jebentancour/Bandonberry/stl/CodificacionDeNombresDePartea.jpg

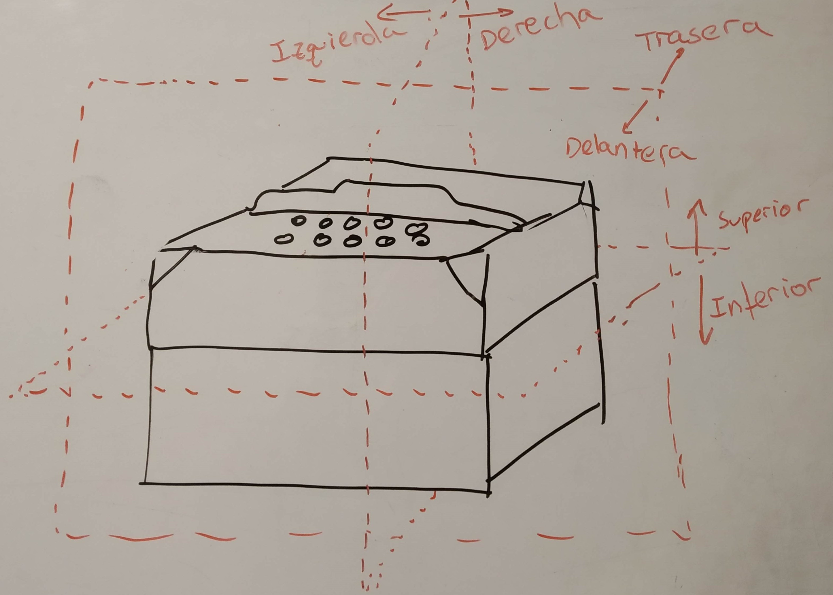
stl/CodificacionDeNombresDePartea.jpg
