jebentancour/Bandonberry/stl/FotosConMedidas/FotoMedida2.png

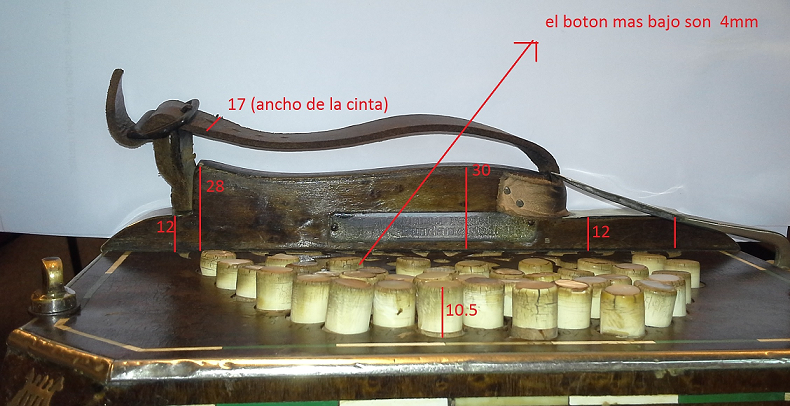
stl/FotosConMedidas/FotoMedida2.png
