jebentancour/Bandonberry/stl/FotosConMedidas/FotoMedida7.png

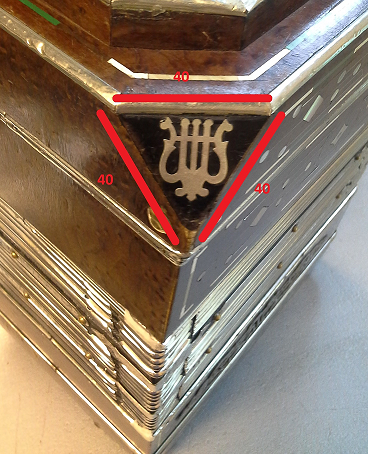
stl/FotosConMedidas/FotoMedida7.png
