jebentancour/Bandonberry/stl/FotosConMedidas/FotoMedida8.png

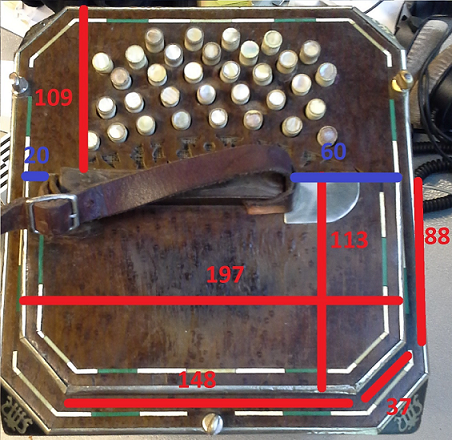
stl/FotosConMedidas/FotoMedida8.png
