jebentancour/Bandonberry/stl/STL_Tapa_Derecha/Botonera.stl

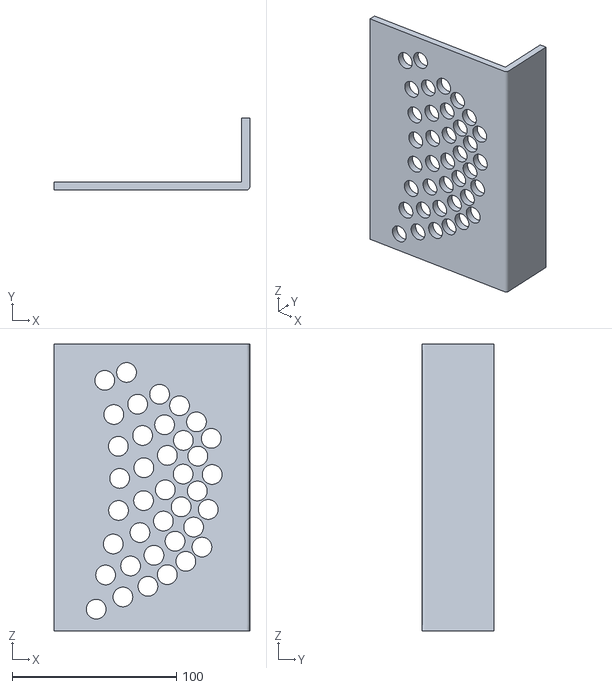
[picture p38: CAD file, 2019-04-07]
stl/STL_Tapa_Derecha/Botonera.stl
119.0 x 43.8 x 174.6
