jebentancour/Bandonberry/stl/STL_Tapa_Izquierda/EsqInfDelIzq.stl

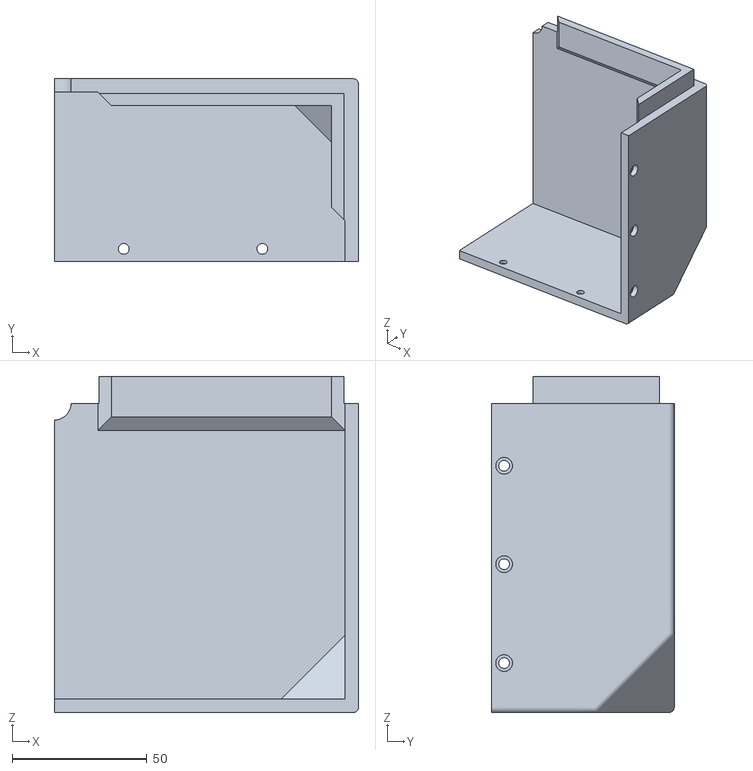
[picture p39: CAD file, 2019-04-07]
stl/STL_Tapa_Izquierda/EsqInfDelIzq.stl
112.9 x 67.8 x 124.8
