jebentancour/Bandonberry/stl/Agarres_Botones/Agarres/AgarreTuercaSimple.stl

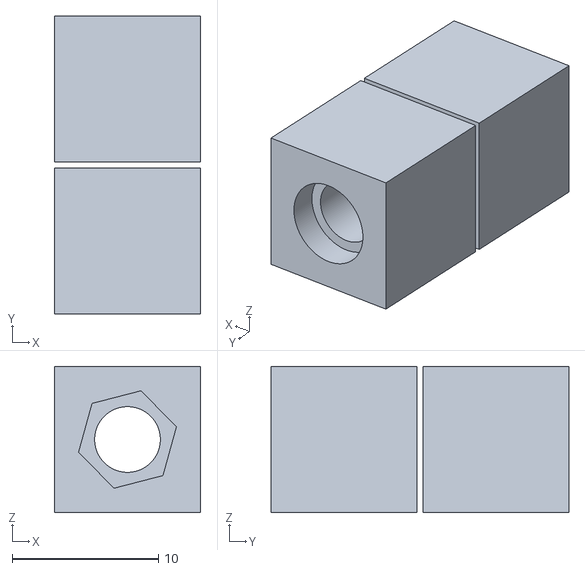
[picture p40: CAD file, 2019-04-07]
stl/Agarres_Botones/Agarres/AgarreTuercaSimple.stl
10.0 x 20.4 x 10.0
