jebentancour/Bandonberry/stl/STL_Tapa_Derecha/EsqIzqTrasInf.stl

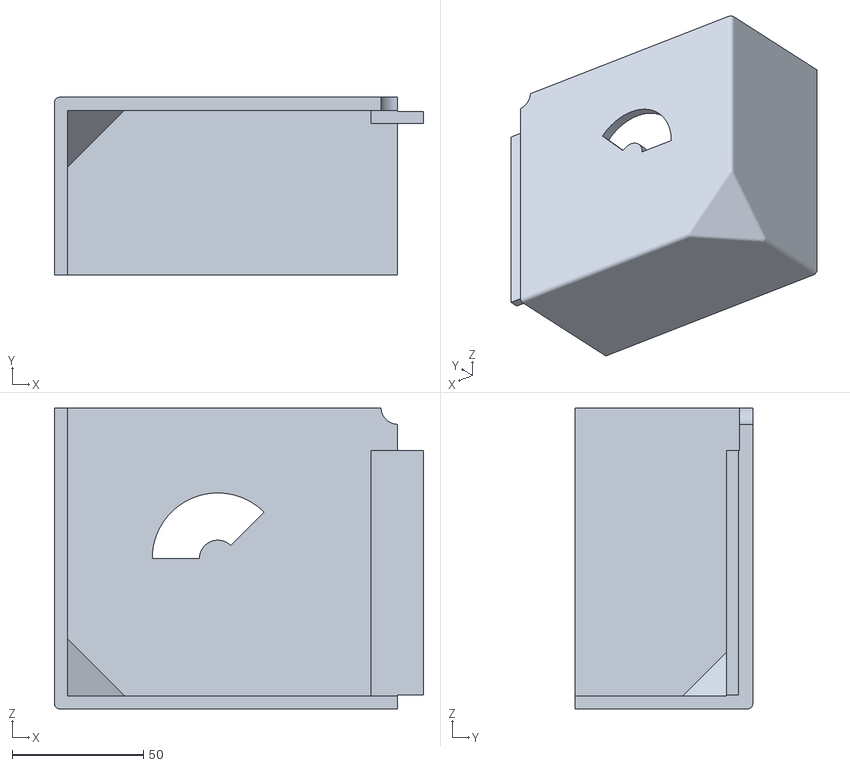
[picture p41: CAD file, 2019-04-07]
stl/STL_Tapa_Derecha/EsqIzqTrasInf.stl
140.8 x 67.8 x 114.8
