jebentancour/Bandonberry/stl/STL_Tapa_Izquierda/EsqSupTrasIzq.stl

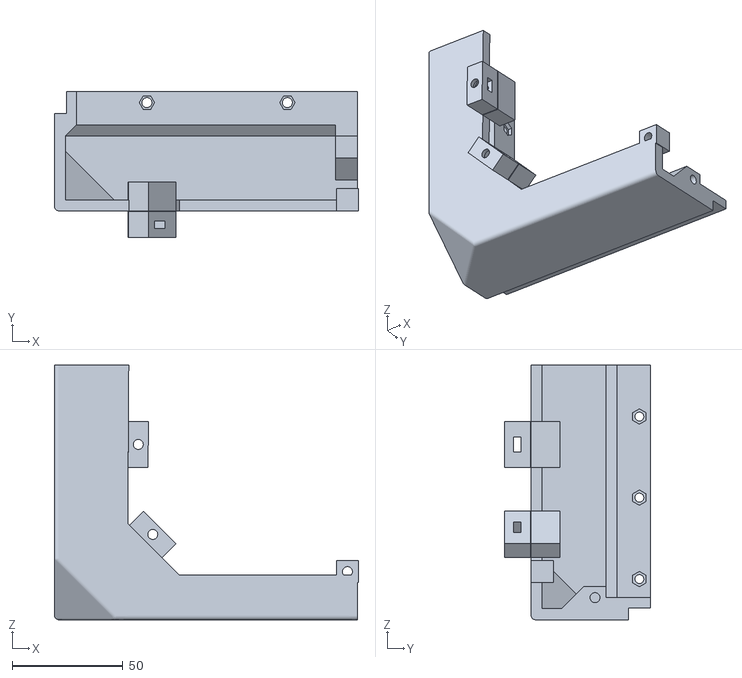
[picture p42: CAD file, 2019-04-07]
stl/STL_Tapa_Izquierda/EsqSupTrasIzq.stl
137.1 x 65.8 x 114.8
