jebentancour/Bandonberry/stl/STL_Tapa_Derecha/EsqDerDelInf.stl

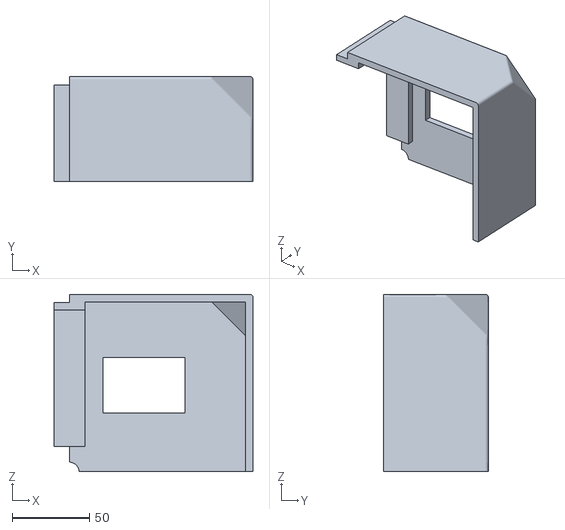
[picture p43: CAD file, 2019-04-07]
stl/STL_Tapa_Derecha/EsqDerDelInf.stl
128.8 x 67.8 x 114.8
