jebentancour/Bandonberry/stl/STL_Tapa_Izquierda/EsqInfDelDer.stl

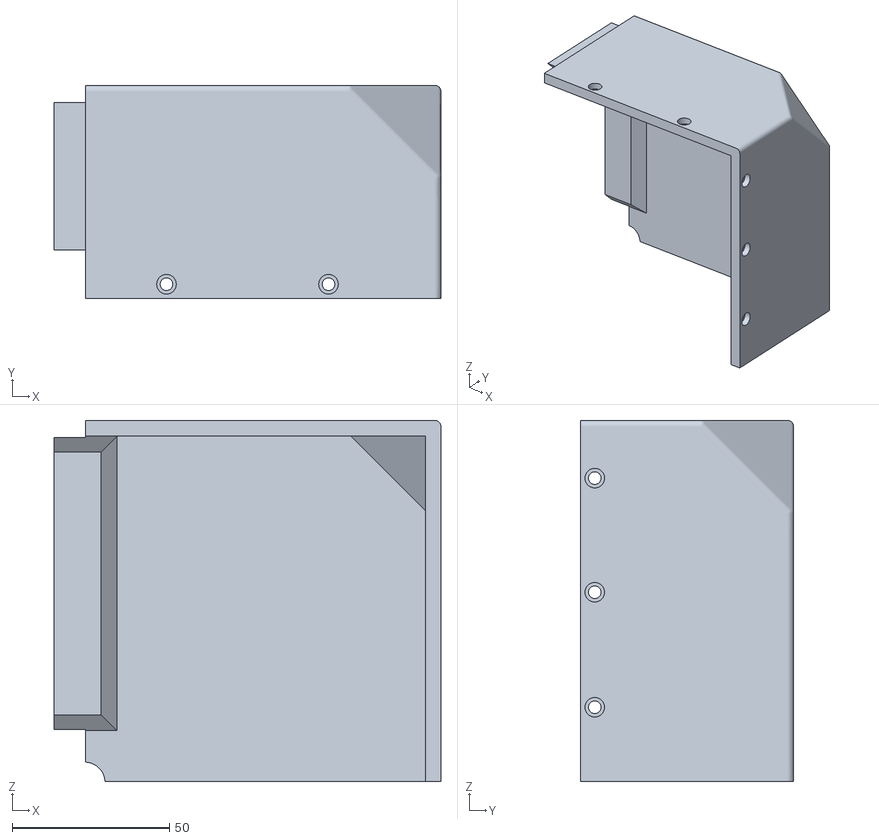
[picture p44: CAD file, 2019-04-07]
stl/STL_Tapa_Izquierda/EsqInfDelDer.stl
122.9 x 67.8 x 114.8
