jebentancour/Bandonberry/stl/STL_Tapa_Derecha/EsqDerTrasInf.stl

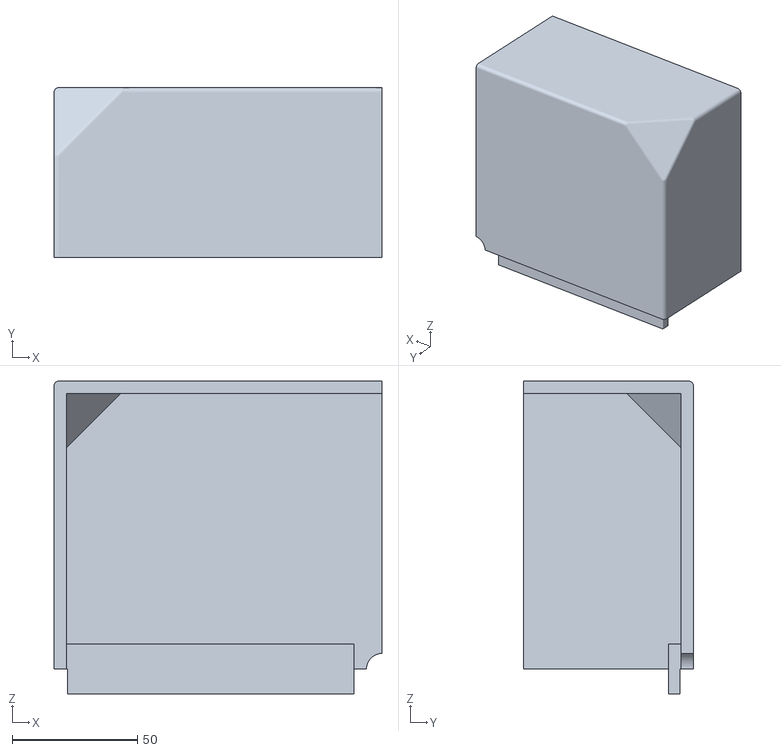
[picture p45: CAD file, 2019-04-07]
stl/STL_Tapa_Derecha/EsqDerTrasInf.stl
130.8 x 67.8 x 124.8
