jebentancour/Bandonberry/stl/STL_Tapa_Izquierda/EsqSupTrasDer.stl

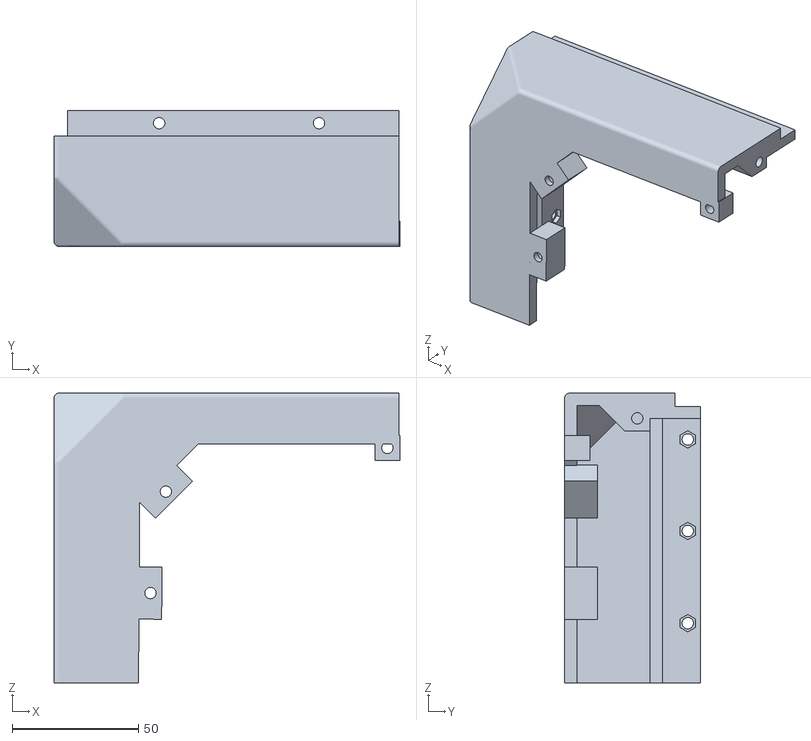
[picture p46: CAD file, 2019-04-07]
stl/STL_Tapa_Izquierda/EsqSupTrasDer.stl
137.1 x 53.8 x 114.8
