jebentancour/Bandonberry/stl/STL_Tapa_Derecha/Palanca.stl

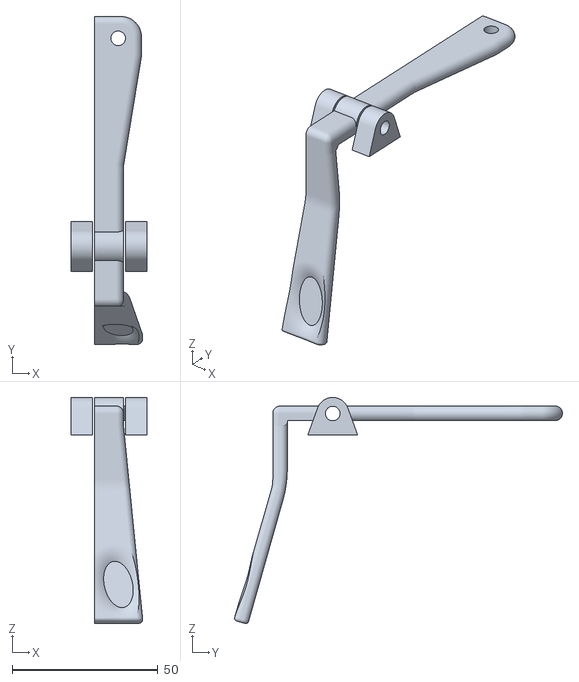
[picture p47: CAD file, 2019-04-07]
stl/STL_Tapa_Derecha/Palanca.stl
26.0 x 112.6 x 77.6
