jebentancour/Bandonberry/stl/STL_Tapa_Izquierda/CajaReson.stl

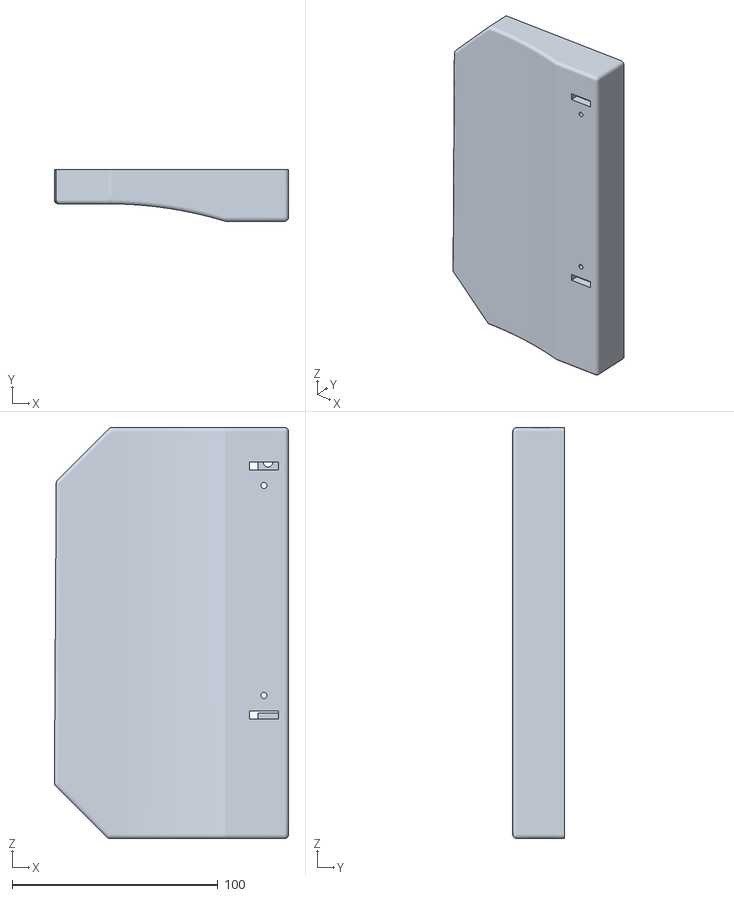
[picture p48: CAD file, 2019-04-07]
stl/STL_Tapa_Izquierda/CajaReson.stl
113.8 x 25.0 x 199.7
