jebentancour/Bandonberry/stl/STL_Tapa_Derecha/EsqDerTrasSup.stl

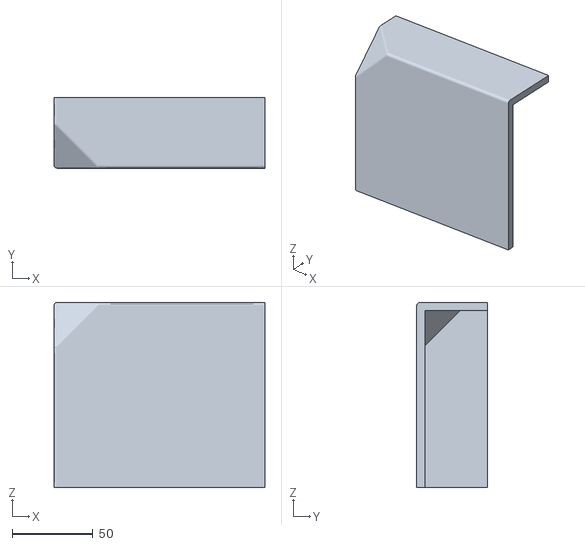
[picture p49: CAD file, 2019-04-07]
stl/STL_Tapa_Derecha/EsqDerTrasSup.stl
131.0 x 43.8 x 115.0
