jebentancour/Bandonberry/stl/STL_Tapa_Izquierda/EsqInfTrasIzq.stl

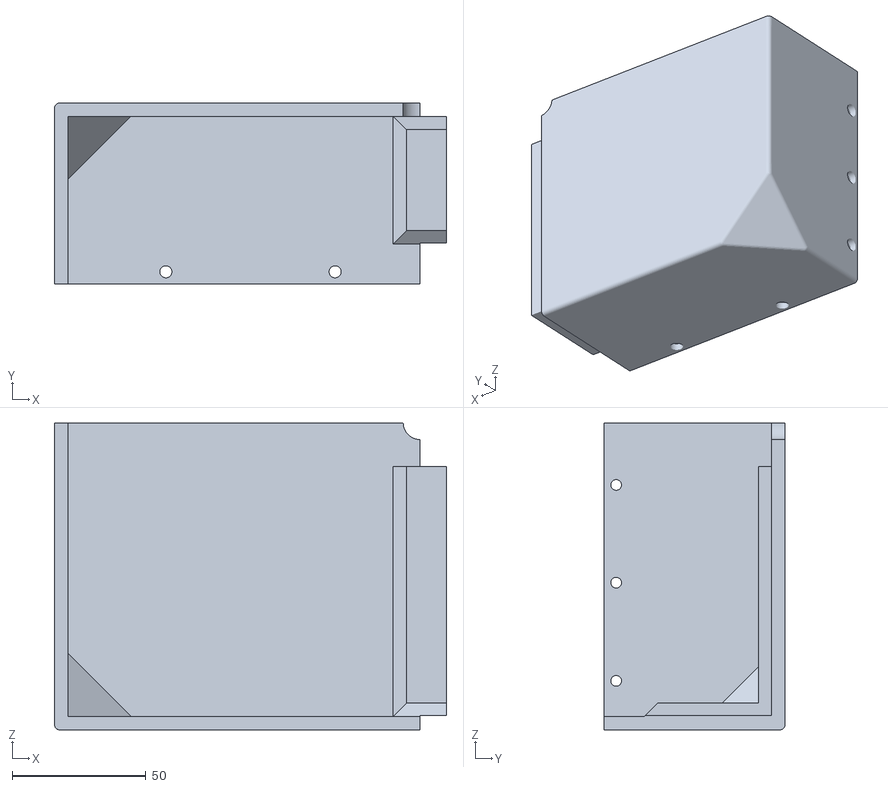
[picture p50: CAD file, 2019-04-07]
stl/STL_Tapa_Izquierda/EsqInfTrasIzq.stl
146.7 x 67.8 x 114.8
