jebentancour/Bandonberry/stl/STL_Tapa_Derecha/EsqIzqTrasSup.stl

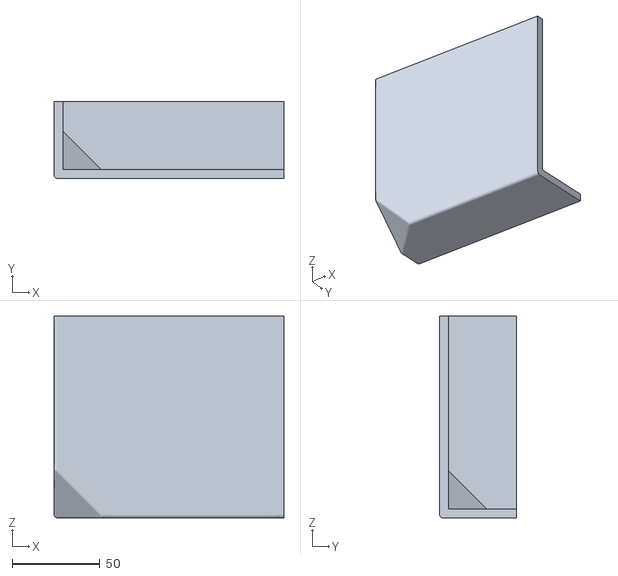
[picture p51: CAD file, 2019-04-07]
stl/STL_Tapa_Derecha/EsqIzqTrasSup.stl
131.0 x 43.8 x 115.0
