jebentancour/Bandonberry/stl/STL_Tapa_Izquierda/Botonera.stl

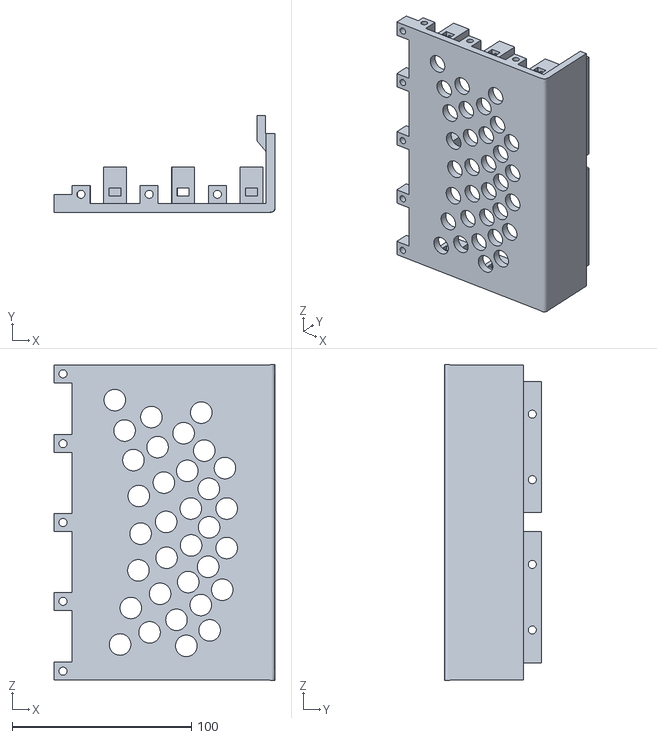
[picture p52: CAD file, 2019-04-07]
stl/STL_Tapa_Izquierda/Botonera.stl
123.1 x 53.8 x 176.1
